astervu/FEELLINK/images/versie 1 schema.png

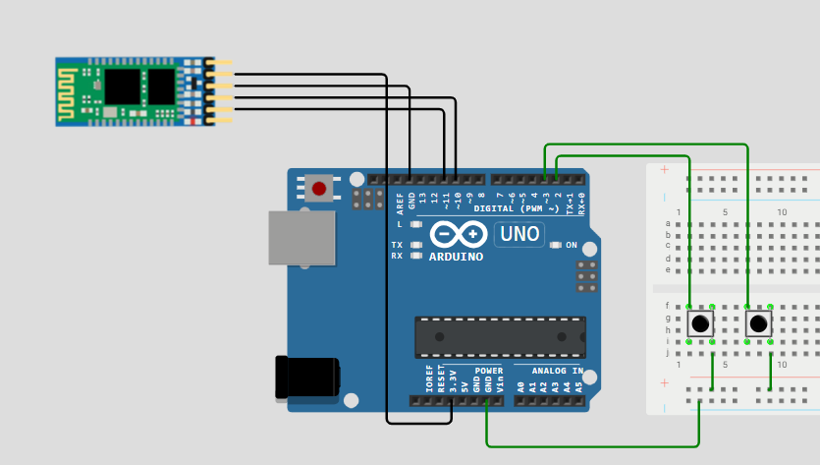
images/versie 1 schema.png
