astervu/FEELLINK/images/versie 6 schema.png

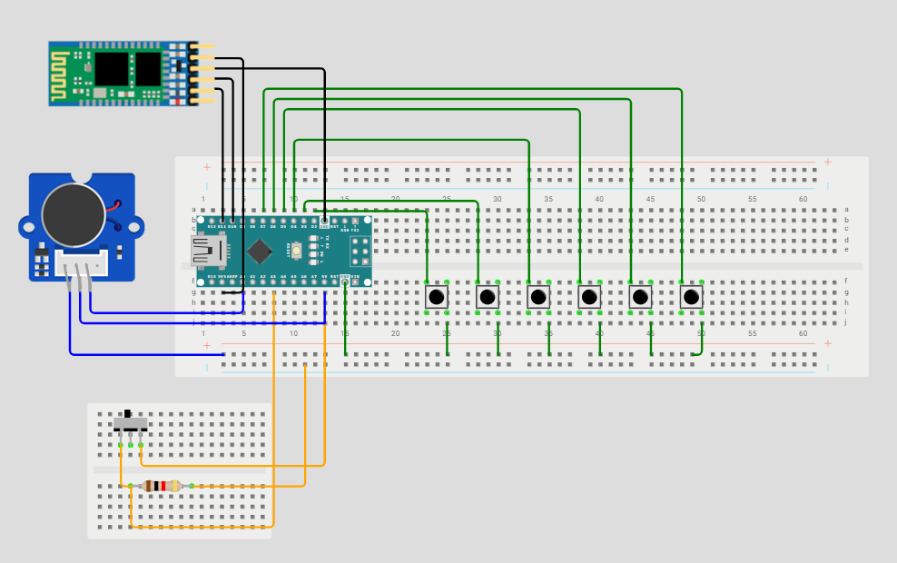
images/versie 6 schema.png
