astervu/FEELLINK/images/versie 7 schema.png

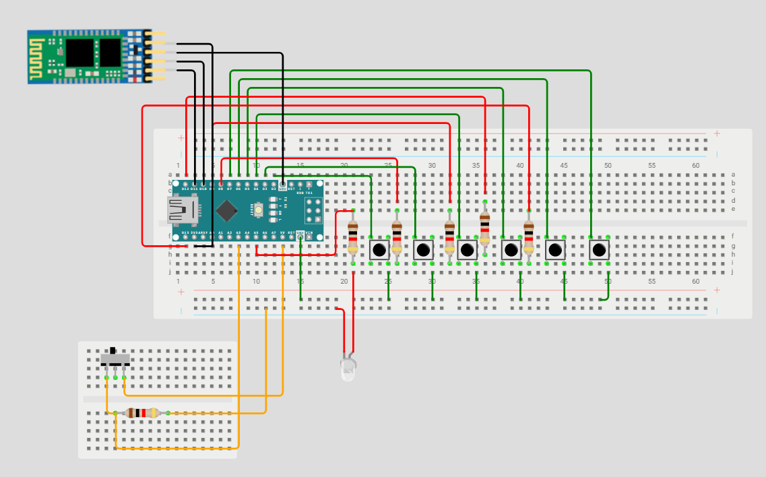
images/versie 7 schema.png
