astervu/FEELLINK/images/versie 8 schema.png

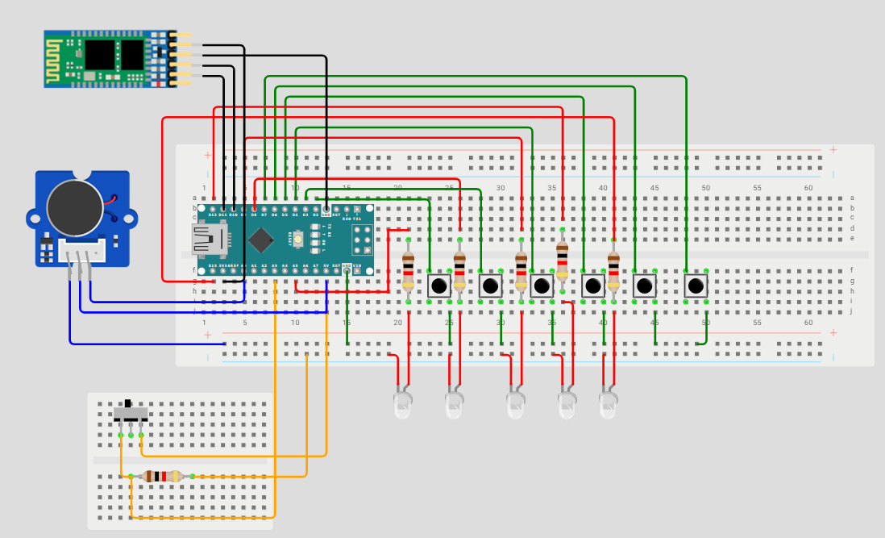
images/versie 8 schema.png
