astervu/FEELLINK/BillOfMaterials/electronica/BOM bedradingsschema.png

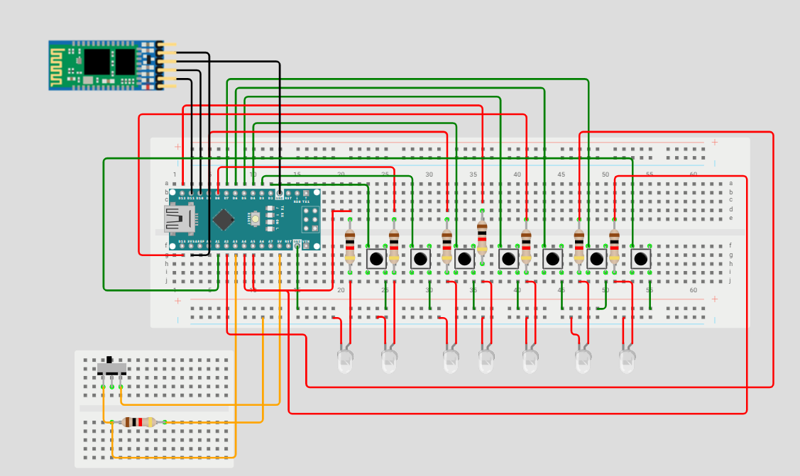
BillOfMaterials/electronica/BOM bedradingsschema.png
