astervu/FEELLINK/BillOfMaterials/leerkracht interfaces/enter classroom.png

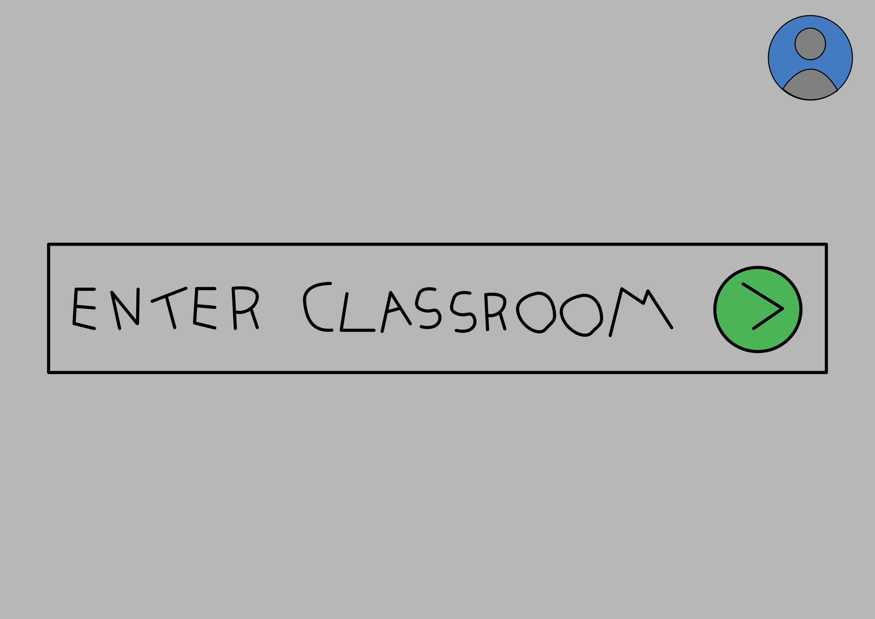
BillOfMaterials/leerkracht interfaces/enter classroom.png
