astervu/FEELLINK/BillOfMaterials/leerkracht interfaces/interface invullen.png

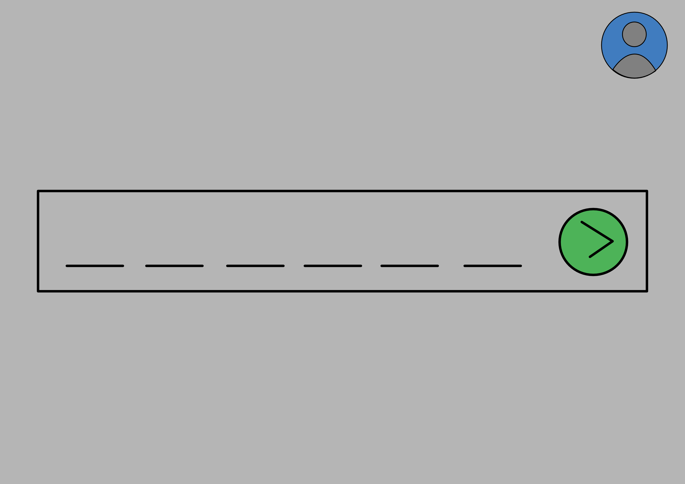
BillOfMaterials/leerkracht interfaces/interface invullen.png
