astervu/FEELLINK/BillOfMaterials/leerkracht interfaces/interface overzicht klaslokaal omgedraaid.png

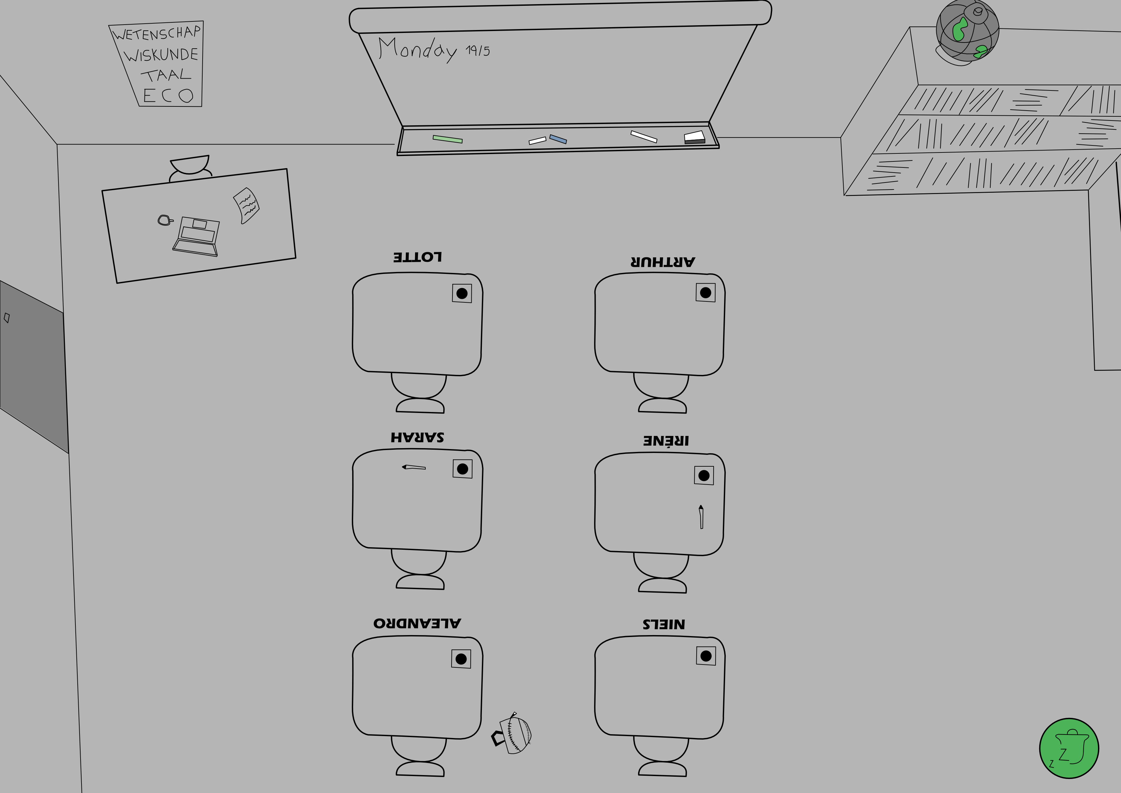
BillOfMaterials/leerkracht interfaces/interface overzicht klaslokaal omgedraaid.png
