astervu/FEELLINK/BillOfMaterials/leerkracht interfaces/persoonlijk.png

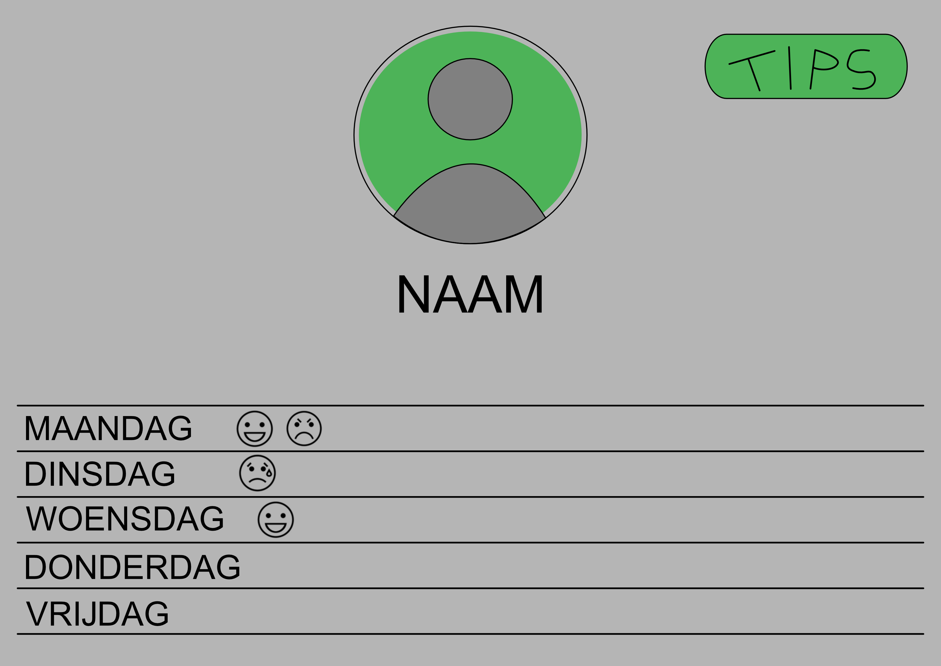
BillOfMaterials/leerkracht interfaces/persoonlijk.png
