astervu/FEELLINK/BillOfMaterials/leerkracht interfaces/snooze.png

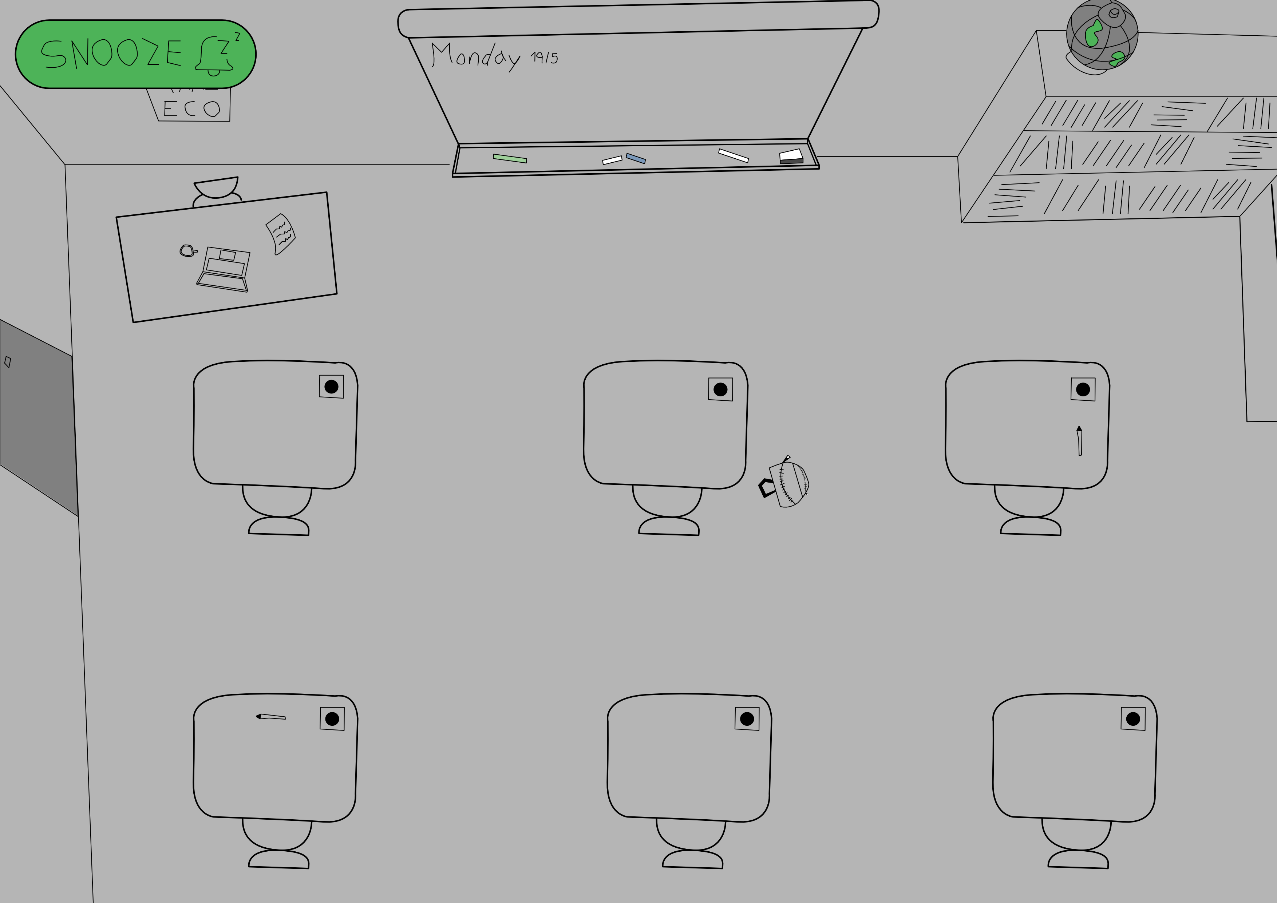
BillOfMaterials/leerkracht interfaces/snooze.png
