astervu/FEELLINK/BillOfMaterials/leerkracht interfaces/timer.png

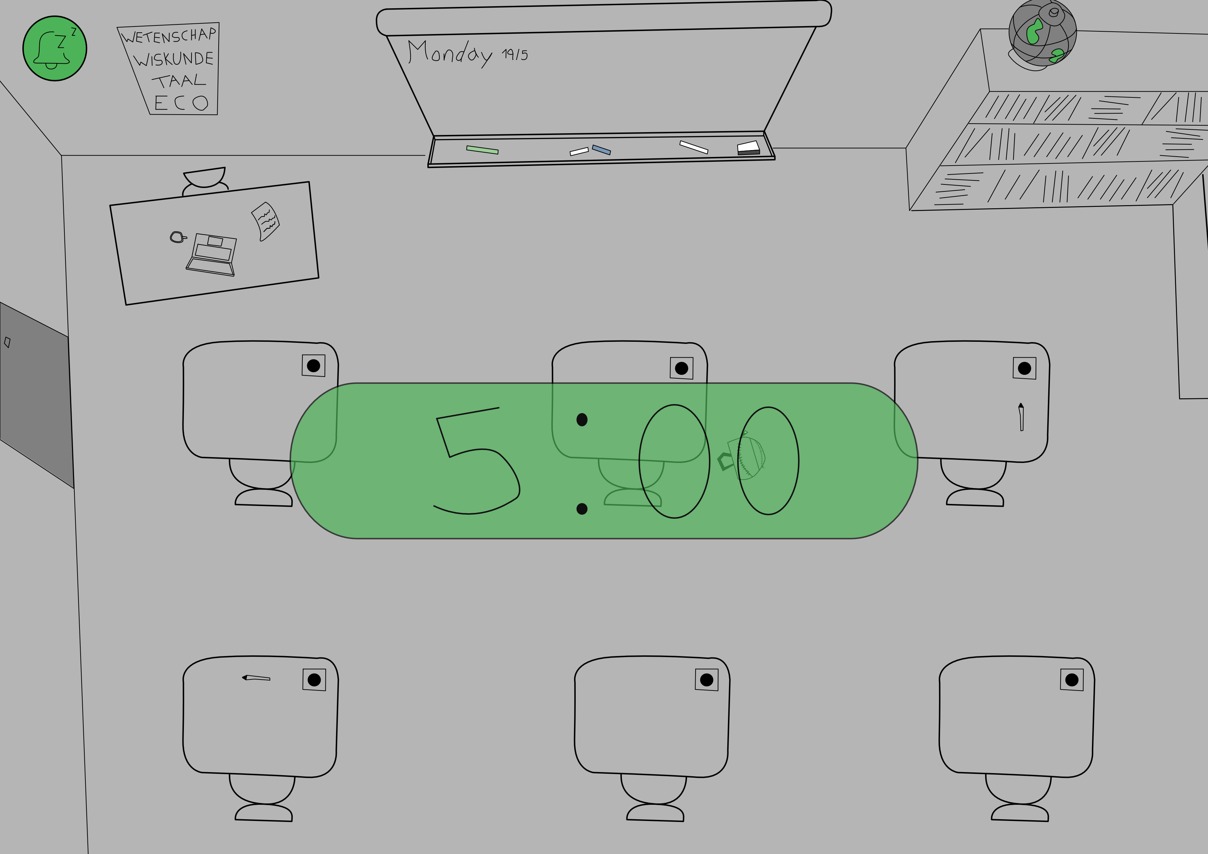
BillOfMaterials/leerkracht interfaces/timer.png
