astervu/FEELLINK/BillOfMaterials/leerkracht interfaces/tips.png

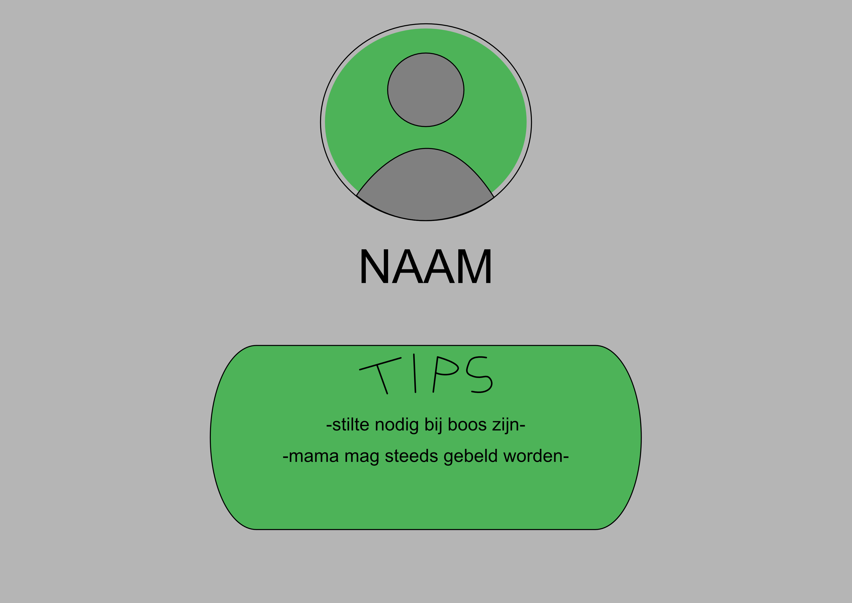
BillOfMaterials/leerkracht interfaces/tips.png
